iragut/OpenBook-Project/Images/1.jpg

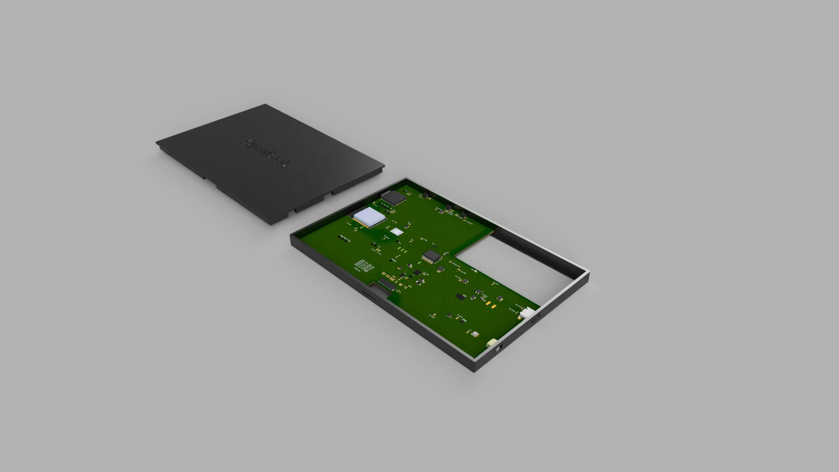
Images/1.jpg
