iragut/OpenBook-Project/Images/2.JPEG

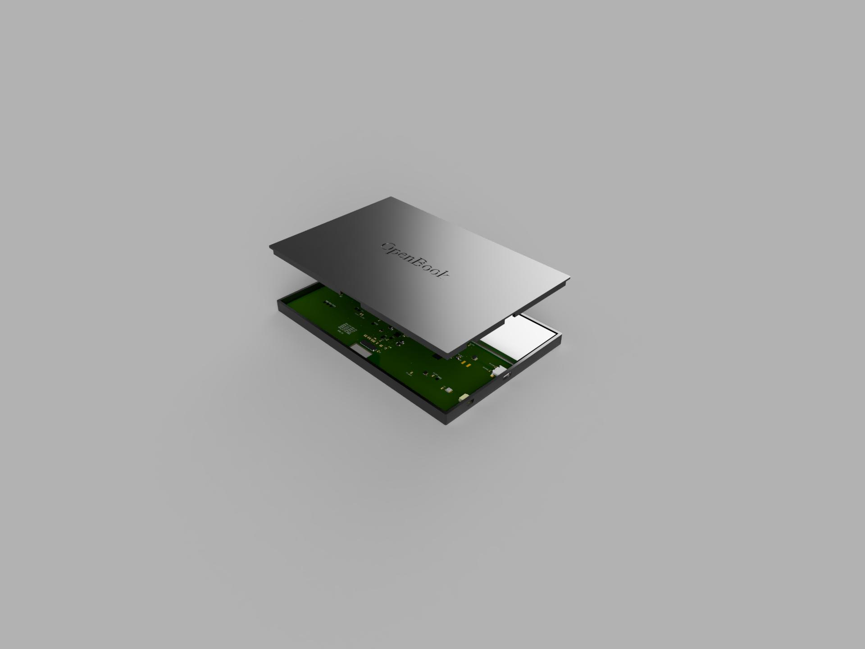
Images/2.JPEG
