iragut/OpenBook-Project/Images/3.jpg

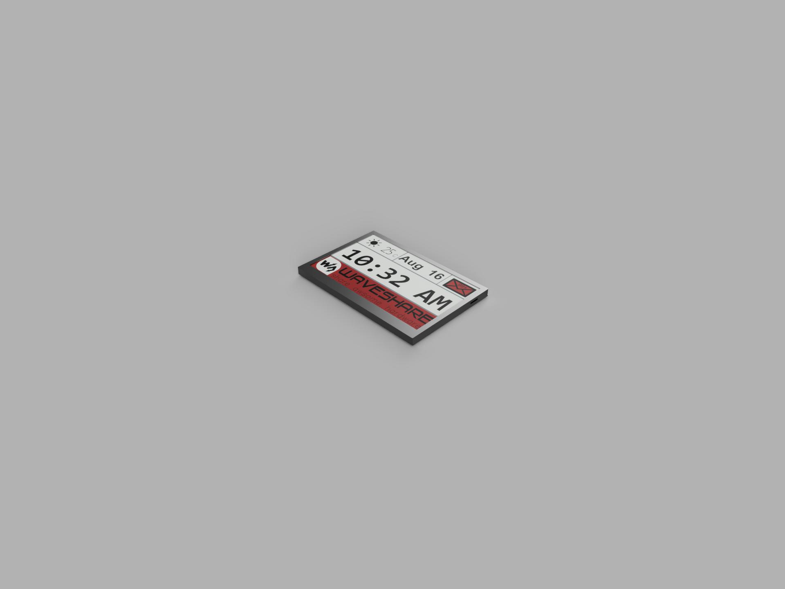
Images/3.jpg
